jjmz/Atari-Quadrature-USB-Mouse-Adapter/doc/gerbers/2023-06-19 16_37_49-EasyEDA(Standard) 6.5.22 - Team Work mode.png

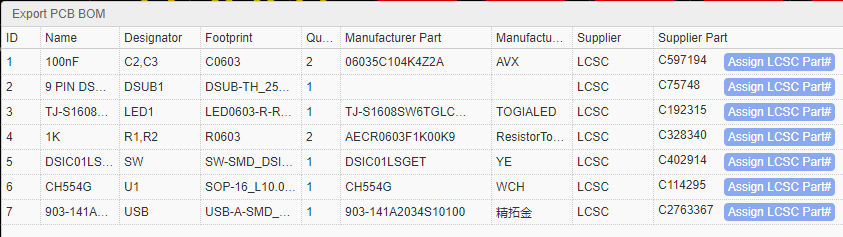
doc/gerbers/2023-06-19 16_37_49-EasyEDA(Standard) 6.5.22 - Team Work mode.png
