jjmz/Atari-Quadrature-USB-Mouse-Adapter/doc/IMG_20210318_133215.jpg

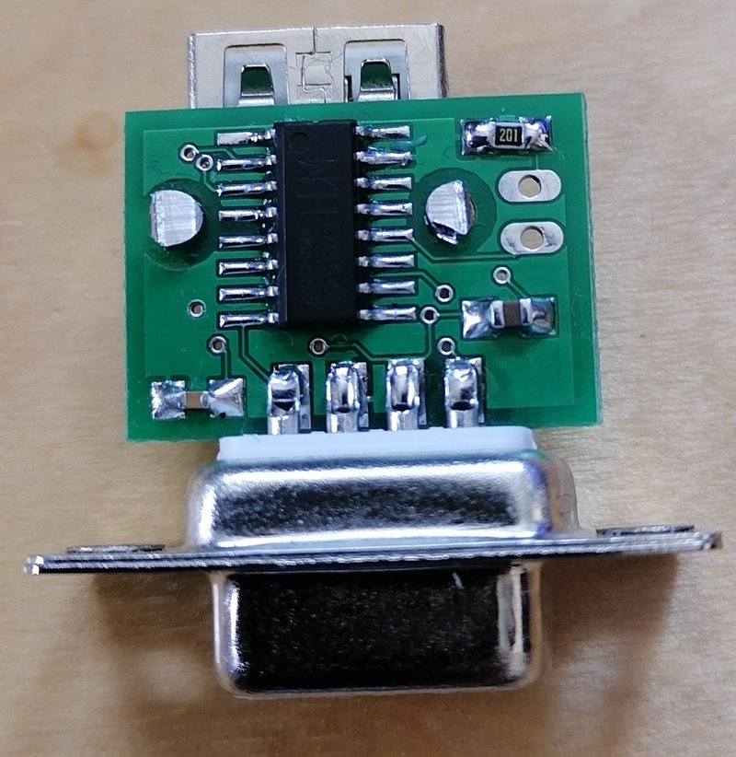
doc/IMG_20210318_133215.jpg
